kristianhentschel/tildagon-matrix-hexpansion/firmware/lite_loop/leds.h

#ifndef LEDS_H
#define LEDS_H

// Generated from lite-loop.kicad_pcb at 2026-06-24T19:48:48.578917
// Connector J1 at Vector2(150000000, 91500000), Angle(0.0)
// Badge origin at Vector2(150000000, 50000000)

#define LEDS_COUNT 156
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

typedef struct polar_position {
  uint8_t radius;
  float angle;
} polar_position_t;

extern const polar_position_t leds_polar_positions[LEDS_COUNT];

#define LEDS_GRID_COLS 18
#define LEDS_GRID_ROWS 9
#define LEDS_GRID_INDICES {255, 255, 255, 0, 1, 2, 3, 4, 5, 6, 7, 8, 9, 10, 11, 255, 255, 255, 12, 13, 14, 15, 16, 17, 18, 19, 20, 21, 22, 23, 114, 115, 116, 117, 118, 119, 24, 25, 26, 27, 28, 29, 30, 31, 32, 33, 34, 35, 126, 127, 128, 129, 130, 131, 36, 37, 38, 39, 40, 41, 42, 43, 44, 45, 46, 47, 138, 139, 140, 141, 142, 143, 48, 49, 50, 51, 52, 53, 54, 55, 56, 57, 58, 59, 150, 151, 152, 153, 154, 155, 60, 61, 62, 63, 64, 65, 66, 67, 68, 69, 70, 71, 108, 109, 110, 111, 112, 113, 72, 73, 74, 75, 76, 77, 78, 79, 80, 81, 82, 83, 120, 121, 122, 123, 124, 125, 84, 85, 86, 87, 88, 89, 90, 91, 92, 93, 94, 95, 132, 133, 134, 135, 136, 137, 96, 97, 98, 99, 100, 101, 102, 103, 104, 105, 106, 107, 144, 145, 146, 147, 148, 149}

extern const uint8_t leds_grid_indices[LEDS_GRID_COLS * LEDS_GRID_ROWS];
#endif
